CUHK-BRME/OMEGA/Hardware/CAD/power hub.STEP

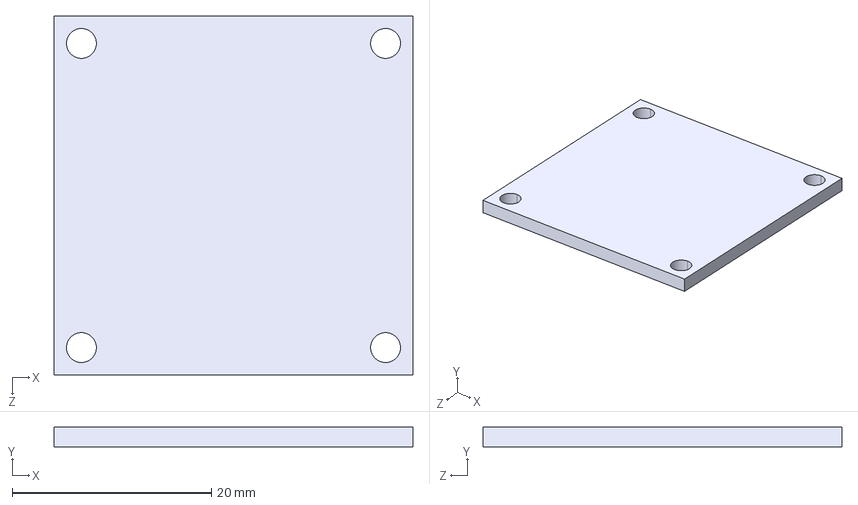
[picture p15: CAD file, 2024-05-09]
Hardware/CAD/power hub.STEP
36.0 x 2.00 x 36.0 mm
