CUHK-BRME/OMEGA/Hardware/CAD/685 bearing.STEP

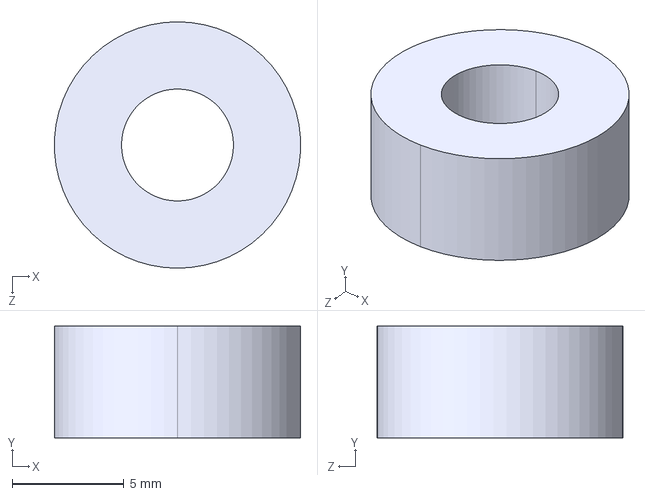
[picture p16: CAD file, 2024-05-09]
Hardware/CAD/685 bearing.STEP
11.0 x 5.00 x 11.0 mm
