CUHK-BRME/OMEGA/Hardware/CAD/battery mount.STEP

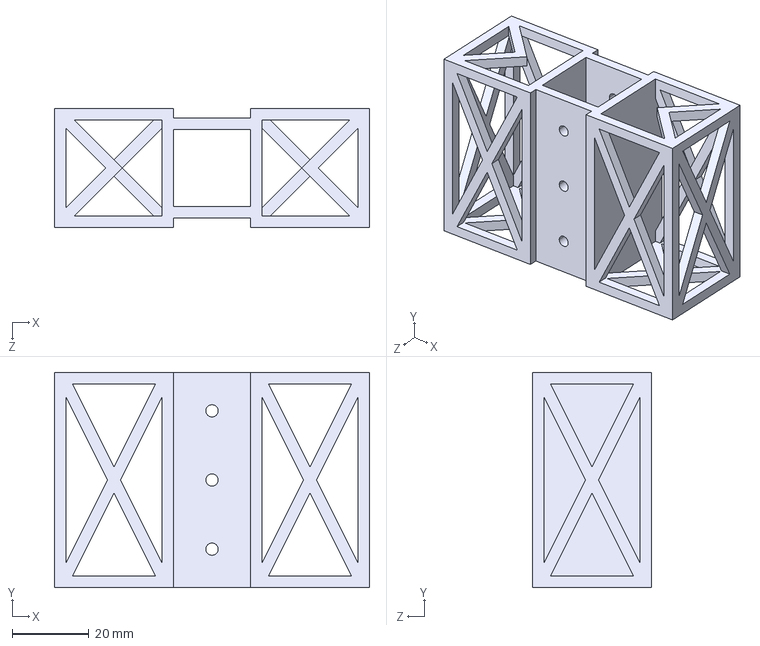
[picture p17: CAD file, 2024-05-09]
Hardware/CAD/battery mount.STEP
82.0 x 56.0 x 31.0 mm
