CUHK-BRME/OMEGA/Hardware/CAD/leg motor mount v3 spacer.STEP

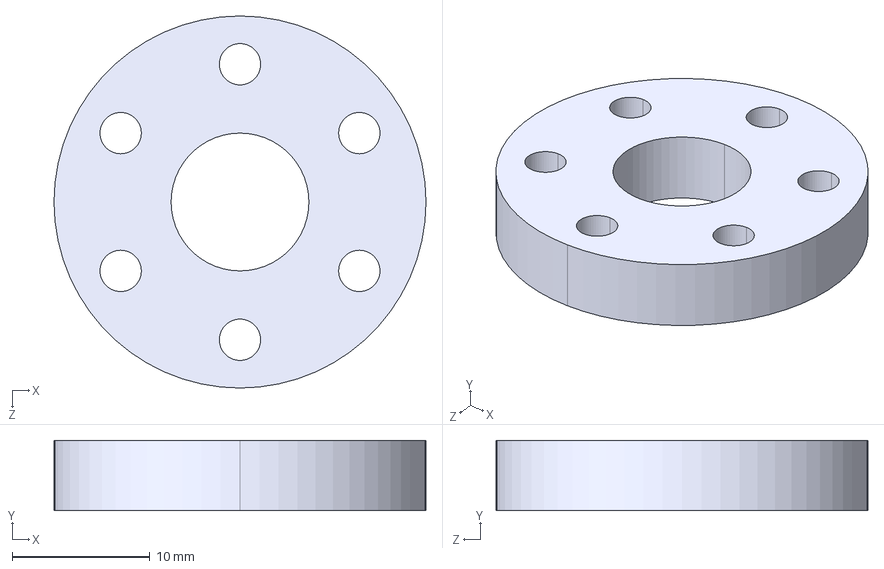
[picture p18: CAD file, 2024-05-09]
Hardware/CAD/leg motor mount v3 spacer.STEP
27.0 x 5.10 x 27.0 mm
