CUHK-BRME/OMEGA/Hardware/CAD/CFplate-motor mount v2 3.STEP

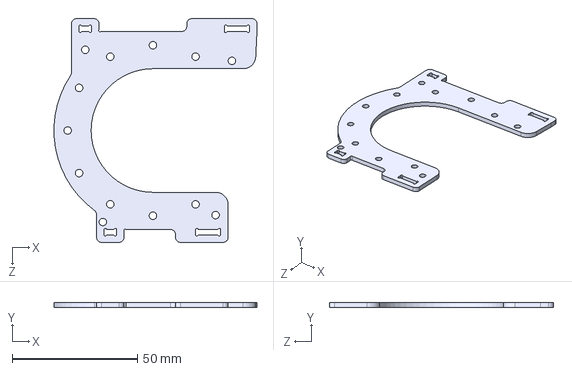
[picture p19: CAD file, 2024-05-09]
Hardware/CAD/CFplate-motor mount v2 3.STEP
81.0 x 2.10 x 89.2 mm
