CUHK-BRME/OMEGA/Hardware/CAD/leg motor mount v3 1 .STEP

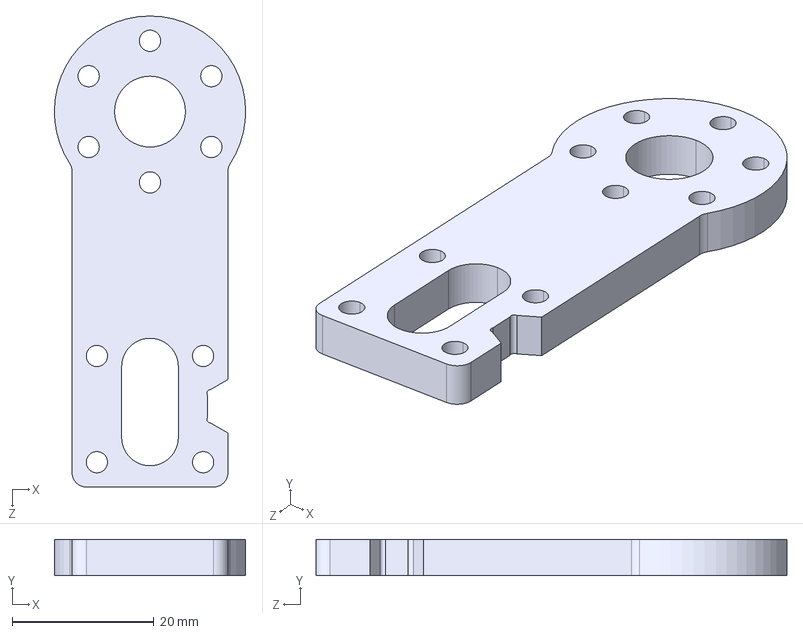
[picture p20: CAD file, 2024-05-09]
Hardware/CAD/leg motor mount v3 1 .STEP
27.0 x 5.10 x 66.5 mm
