CUHK-BRME/OMEGA/Hardware/CAD/CFplate-hipbottom v2.STEP

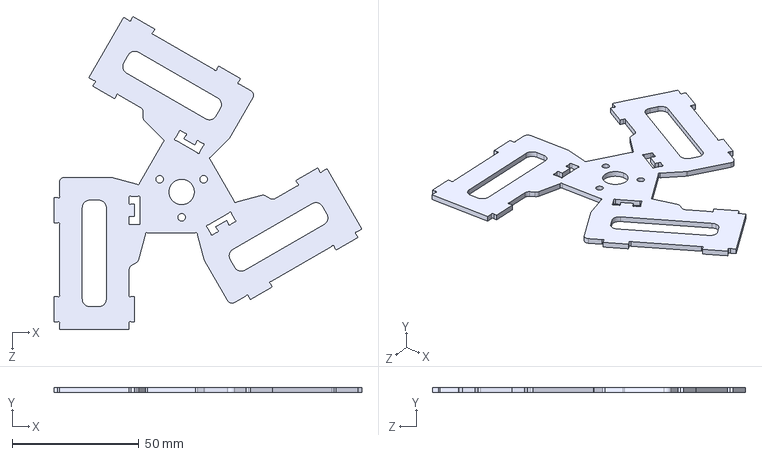
[picture p21: CAD file, 2024-05-09]
Hardware/CAD/CFplate-hipbottom v2.STEP
121.4 x 2.10 x 123.4 mm
