CUHK-BRME/OMEGA/Hardware/CAD/rpi4B.STEP

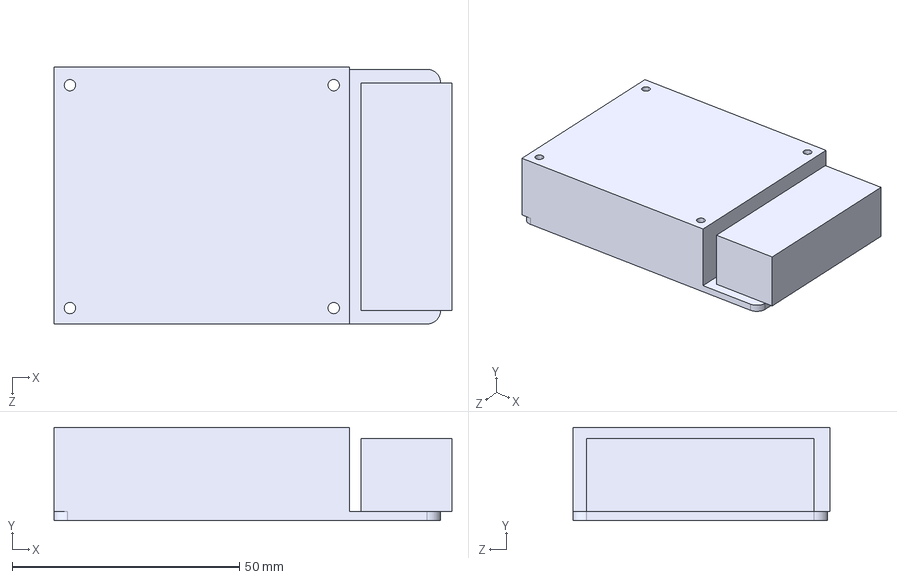
[picture p22: CAD file, 2024-05-09]
Hardware/CAD/rpi4B.STEP
87.5 x 20.5 x 56.5 mm
