CUHK-BRME/OMEGA/Hardware/CAD/electronics mount.STEP

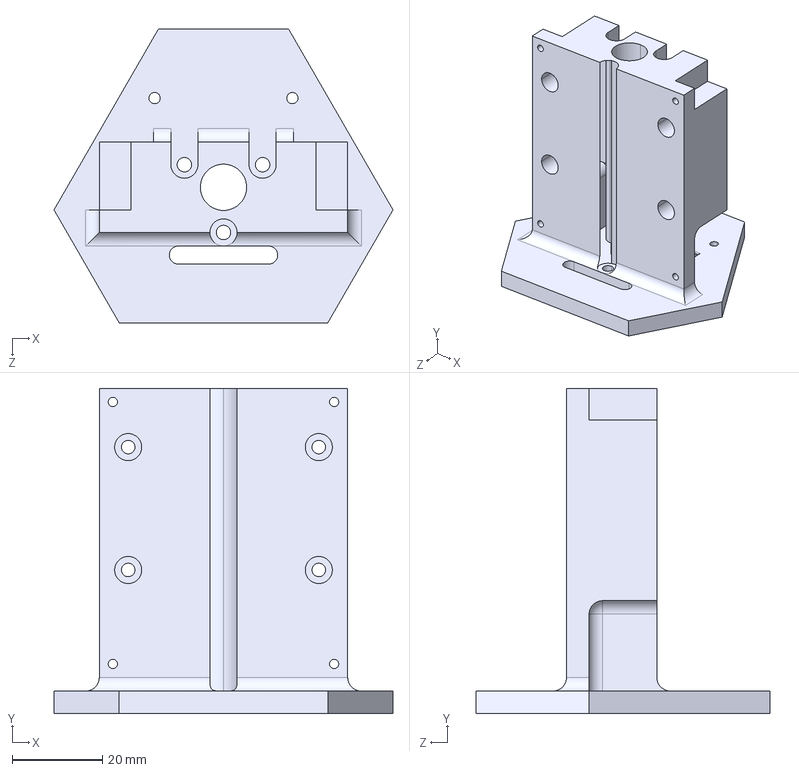
[picture p23: CAD file, 2024-05-09]
Hardware/CAD/electronics mount.STEP
75.1 x 72.0 x 65.0 mm
