CUHK-BRME/OMEGA/Hardware/CAD/CFplate-hiptop v2.STEP

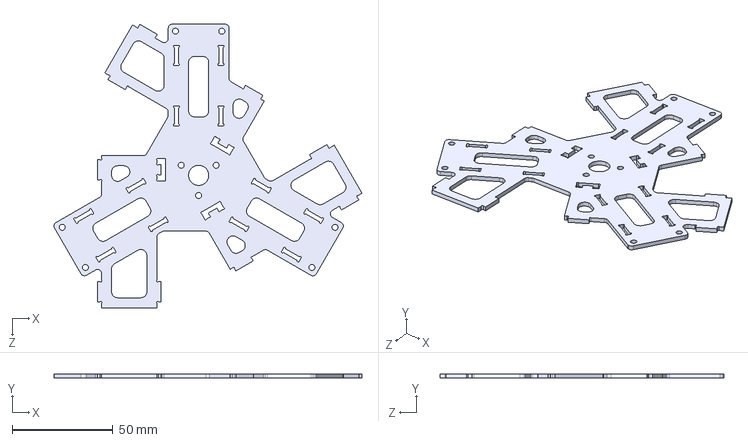
[picture p24: CAD file, 2024-05-09]
Hardware/CAD/CFplate-hiptop v2.STEP
152.8 x 2.10 x 140.7 mm
