CUHK-BRME/OMEGA/Hardware/CAD/thigh knee mount v2.STEP

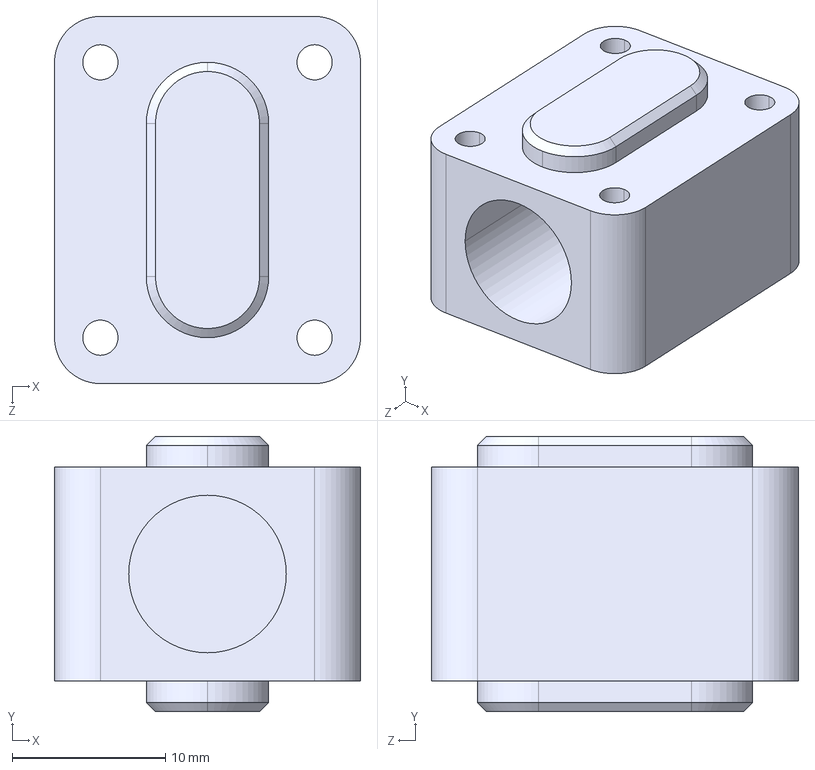
[picture p25: CAD file, 2024-05-09]
Hardware/CAD/thigh knee mount v2.STEP
20.0 x 18.0 x 24.0 mm
