CUHK-BRME/OMEGA/Hardware/CAD/ak60-6v1-1.stp

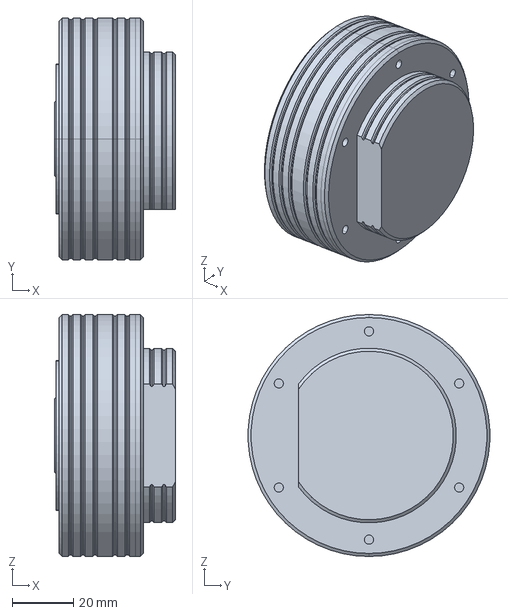
[picture p26: CAD file, 2024-05-09]
Hardware/CAD/ak60-6v1-1.stp
39.5 x 78.9 x 79.0 mm
