CUHK-BRME/OMEGA/Hardware/CAD/knee cross v2.STEP

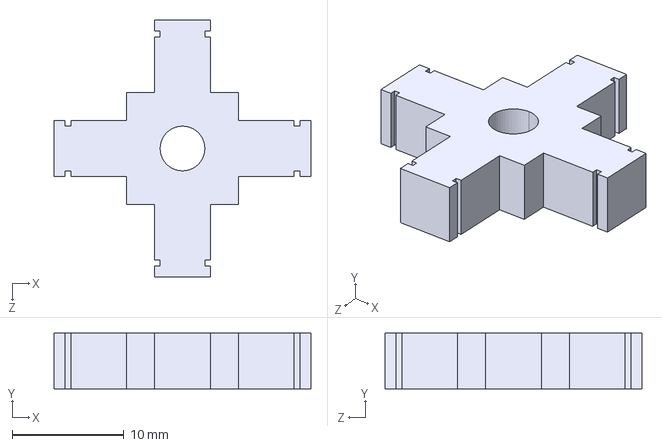
[picture p27: CAD file, 2024-05-09]
Hardware/CAD/knee cross v2.STEP
23.0 x 5.00 x 23.0 mm
