CUHK-BRME/OMEGA/Hardware/CAD/CFtube-103mm thigh.STEP

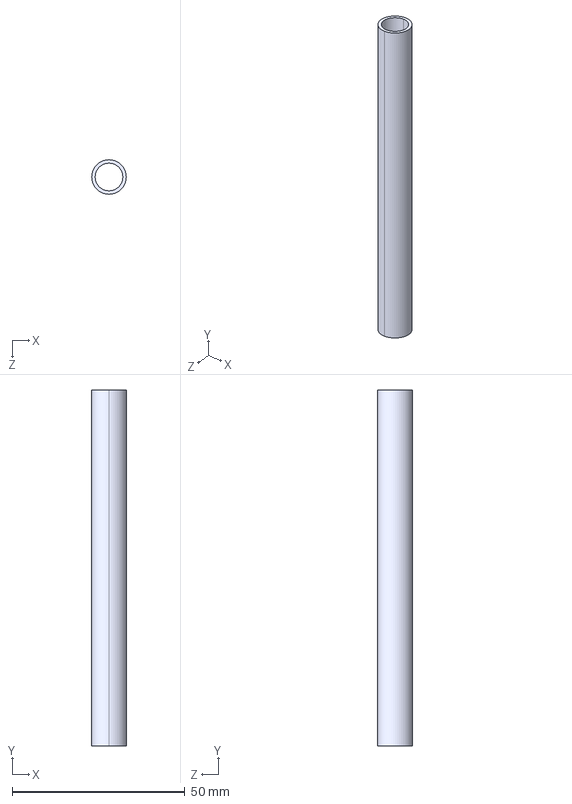
[picture p28: CAD file, 2024-05-09]
Hardware/CAD/CFtube-103mm thigh.STEP
10.00 x 103.0 x 10.00 mm
