CUHK-BRME/OMEGA/Hardware/CAD/knee shaft mount v2.STEP

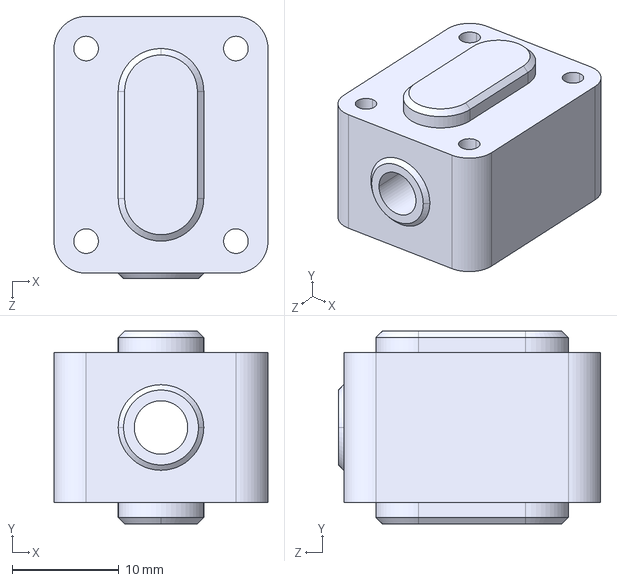
[picture p29: CAD file, 2024-05-09]
Hardware/CAD/knee shaft mount v2.STEP
20.0 x 18.0 x 24.5 mm
