CUHK-BRME/OMEGA/Hardware/CAD/drum knee mount v2.STEP

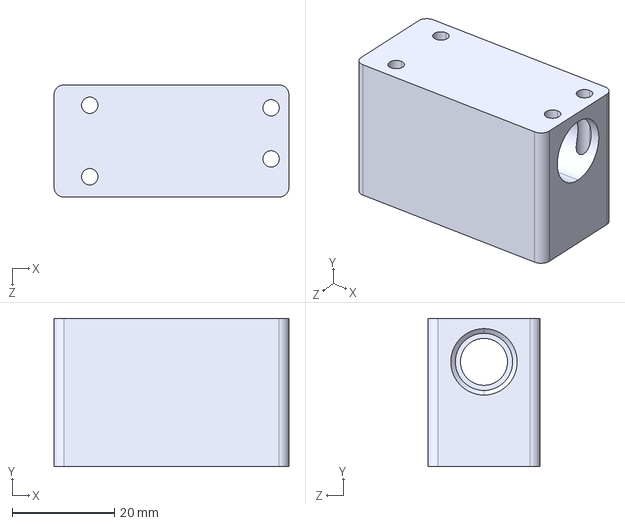
[picture p30: CAD file, 2024-05-09]
Hardware/CAD/drum knee mount v2.STEP
46.0 x 29.0 x 22.0 mm
