CUHK-BRME/OMEGA/Hardware/CAD/handle.STEP

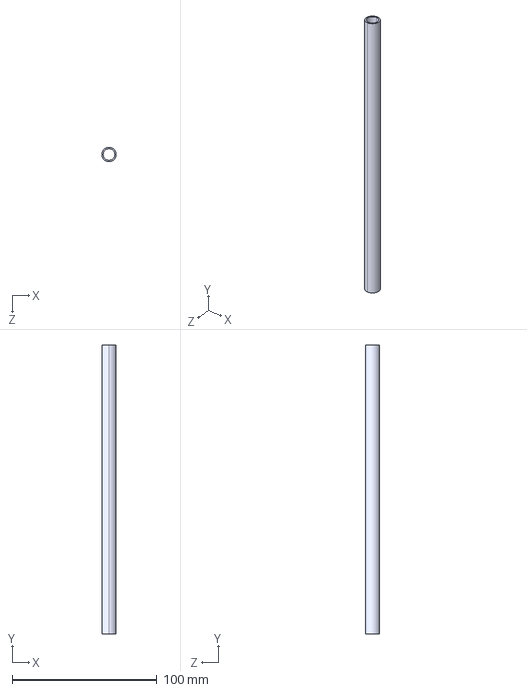
[picture p31: CAD file, 2024-05-09]
Hardware/CAD/handle.STEP
10.00 x 200.0 x 10.00 mm
