CUHK-BRME/OMEGA/Hardware/CAD/CFtube-381mm drum.STEP

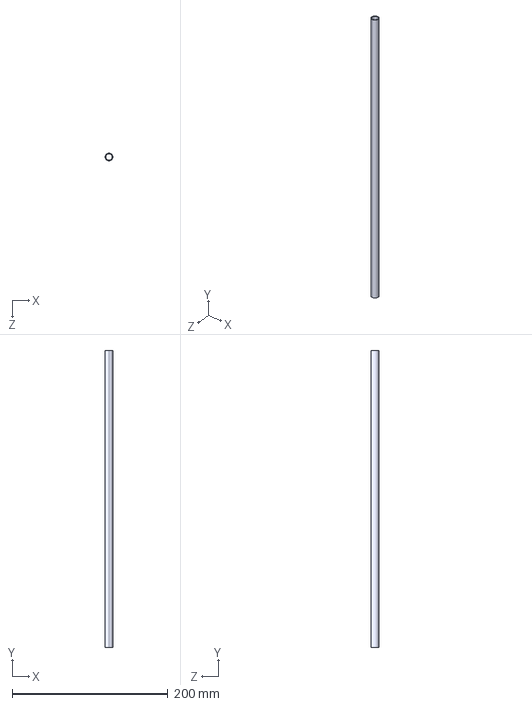
[picture p32: CAD file, 2024-05-09]
Hardware/CAD/CFtube-381mm drum.STEP
10.00 x 381.0 x 10.00 mm
