CUHK-BRME/OMEGA/Hardware/CAD/CFtube-20x20x600mm arm.STEP

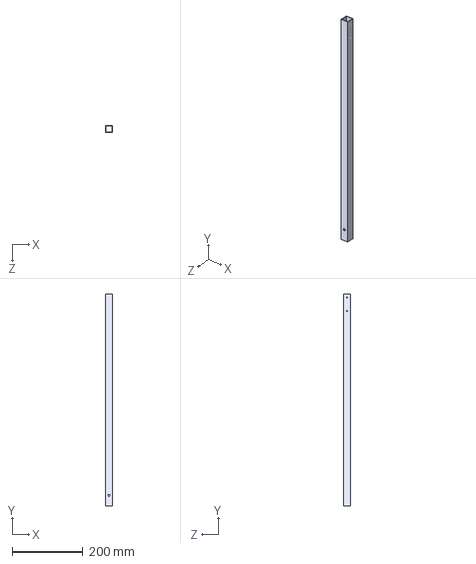
[picture p33: CAD file, 2024-05-09]
Hardware/CAD/CFtube-20x20x600mm arm.STEP
20.0 x 600.0 x 20.0 mm
