CUHK-BRME/OMEGA/Hardware/CAD/knee plate v2.STEP

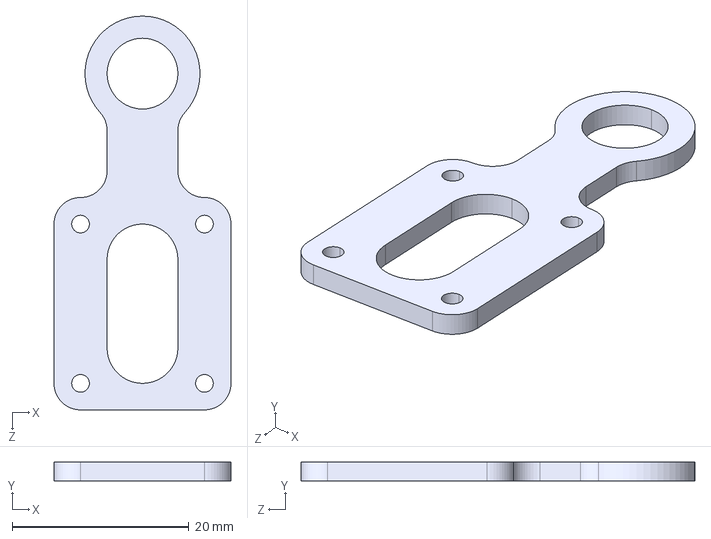
[picture p34: CAD file, 2024-05-09]
Hardware/CAD/knee plate v2.STEP
20.0 x 2.10 x 44.5 mm
