CUHK-BRME/OMEGA/Hardware/CAD/arduino nano.STEP

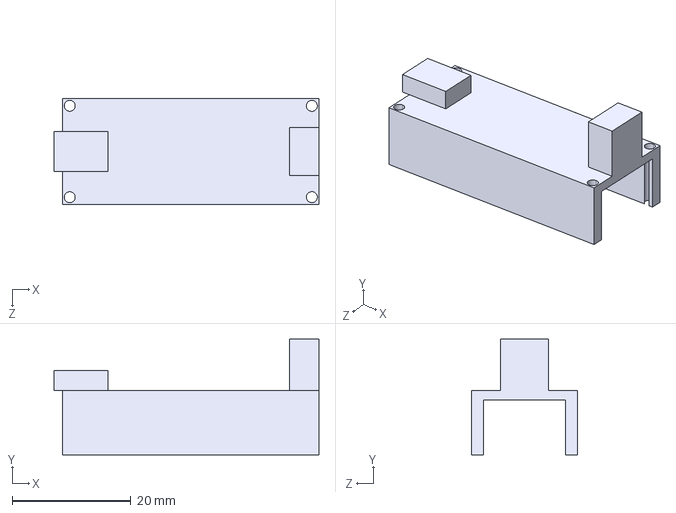
[picture p35: CAD file, 2024-05-09]
Hardware/CAD/arduino nano.STEP
44.6 x 19.5 x 17.8 mm
