CUHK-BRME/OMEGA/Hardware/CAD/foot1 v2.STEP

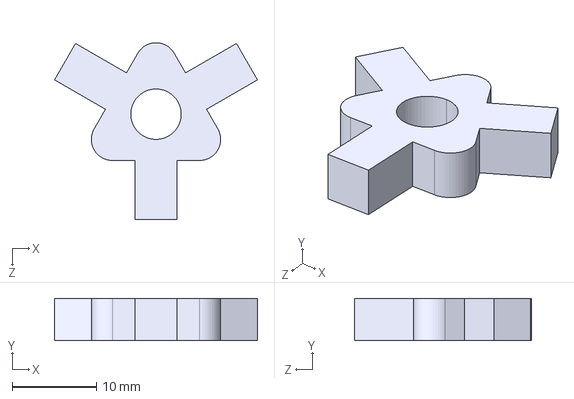
[picture p36: CAD file, 2024-05-09]
Hardware/CAD/foot1 v2.STEP
24.2 x 5.00 x 21.0 mm
