CUHK-BRME/OMEGA/Hardware/CAD/hip bottom leg stopper v2.STEP

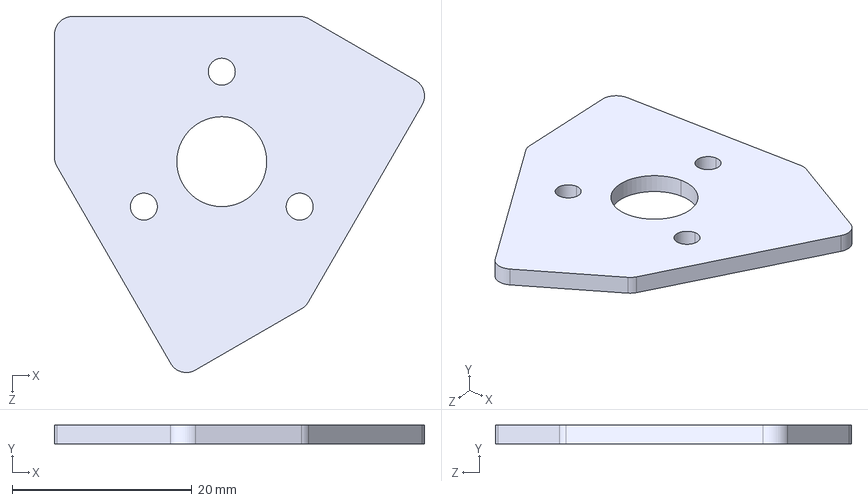
[picture p37: CAD file, 2024-05-09]
Hardware/CAD/hip bottom leg stopper v2.STEP
41.1 x 2.10 x 39.6 mm
