CUHK-BRME/OMEGA/Software/Matlab/MotorPack/can_bus_multi/src/can_bus_test3_ert_rtw/MW_target_hardware_resources.h

#ifndef PORTABLE_WORDSIZES
#ifdef __MW_TARGET_USE_HARDWARE_RESOURCES_H__
#ifndef __MW_TARGET_HARDWARE_RESOURCES_H__
#define __MW_TARGET_HARDWARE_RESOURCES_H__

#define MW_MULTI_TASKING_MODE 1
#include "MW_raspi_init.h"

#define MW_USECODERTARGET 1
#define MW_TARGETHARDWARE Raspberry Pi
#define MW_CONNECTIONINFO_TCPIP_IPADDRESS codertarget.raspi.getDeviceAddress
#define MW_CONNECTIONINFO_TCPIP_PORT 17725
#define MW_CONNECTIONINFO_TCPIP_VERBOSE 1
#define MW_CONNECTIONINFO_TCPIP_RUNINBACKGROUND 1
#define MW_EXTMODE_CONFIGURATION TCP/IP
#define MW_EXTMODE_RUNNING on
#define MW_RTOS Linux
#define MW_RTOSBASERATETASKPRIORITY 40
#define MW_DETECTTASKOVERRUNS 0
#define MW_SCHEDULER_INTERRUPT_SOURCE 0
#define MW_BOARDPARAMETERS_DEVICEADDRESS 192.168.0.193
#define MW_BOARDPARAMETERS_USERNAME pi
#define MW_BOARDPARAMETERS_PASSWORD raspberry
#define MW_BOARDPARAMETERS_BUILDDIR /home/pi
#define MW_RUNTIME_BUILDACTION 1
#define MW_RUNTIME_RUNONBOOT 0
#define MW_SPI_SPI0CE0BUSSPEED 6
#define MW_SPI_SPI0CE1BUSSPEED 6
#define MW_MQTT_BROKERADDRESS mqtt.thingspeak.com
#define MW_MQTT_USERNAME 
#define MW_MQTT_PASSWORD 
#define MW_MQTT_CLIENTID 
#define MW_DATAVERSION 2016.02

#endif /* __MW_TARGET_HARDWARE_RESOURCES_H__ */

#endif

#endif
